Reemuson/ELEC4740-Sensor-Node-2-Board/HTML/images/cat_pdf_drill_map_Sensor-Node-2-Board-PTH_drill_map.png

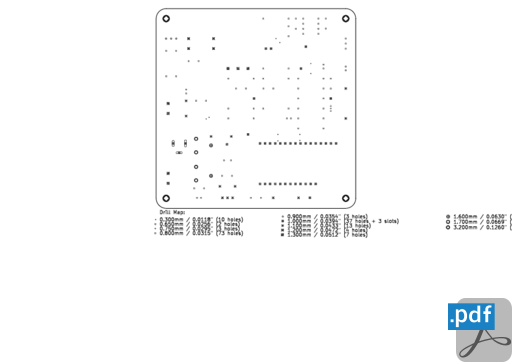
HTML/images/cat_pdf_drill_map_Sensor-Node-2-Board-PTH_drill_map.png
